nojan1/happybox/resources/connections.sch

## EAGLE design resources/connections.sch (2018-11-19)

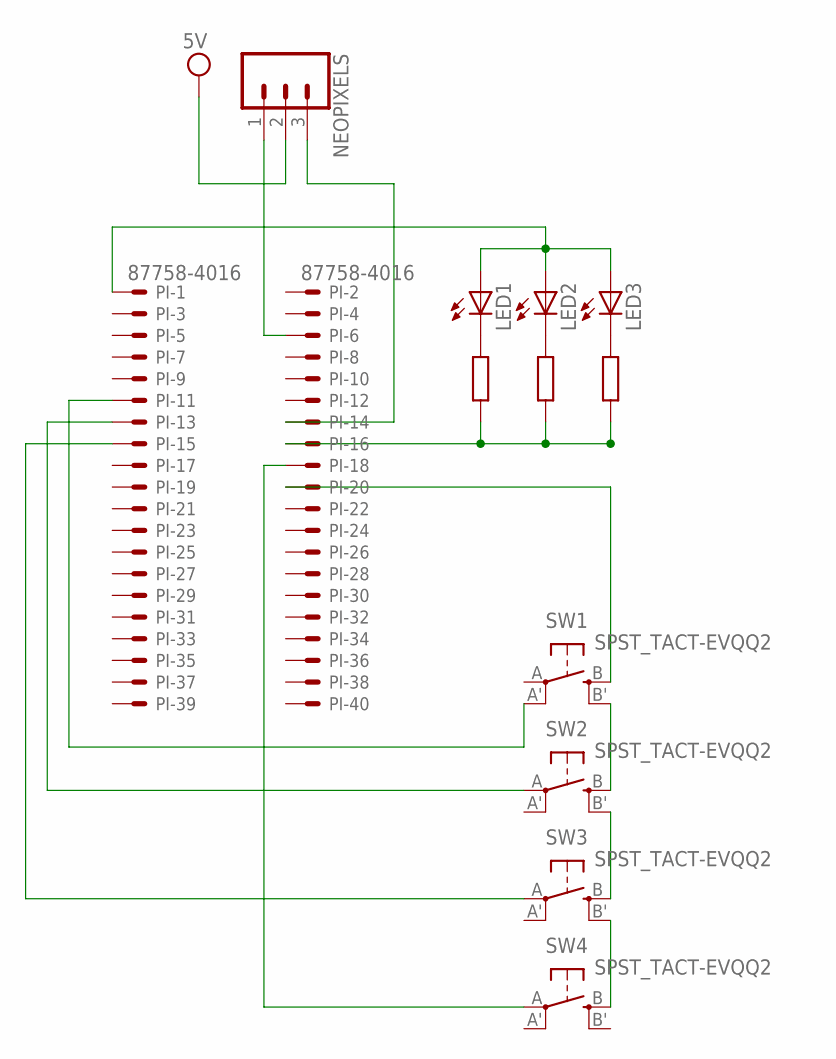
[picture p15: schematic connections.sch]

Parts:
LED1, LED2, LED3: LED3MM
NEOPIXELS: CONN_031X03_NO_SILK; 1X03_NO_SILK
PI: 87758-4016
SW1, SW2, SW3, SW4: SPST_TACT-EVQQ2; EVQ-Q2

Connections:
unnamed: NEOPIXELS.1, PI.6
unnamed: NEOPIXELS.3, PI.14
unnamed: SW1.B' (S1), SW2.B (S)
unnamed: SW2.B' (S1), SW3.B (S)
unnamed: SW3.B' (S1), SW4.B (S)
unnamed: PI.20, SW1.B (S)
unnamed: LED1.A, LED2.A, LED3.A, PI.1
unnamed: PI.11, SW1.A' (P1)
unnamed: PI.13, SW2.A
unnamed: PI.15, SW3.A
unnamed: PI.18, SW4.A
VCC: NEOPIXELS.2
